IstiaMecatroniqueClub/US_Board/documentation/html/class_hcsr04__coll__graph.png

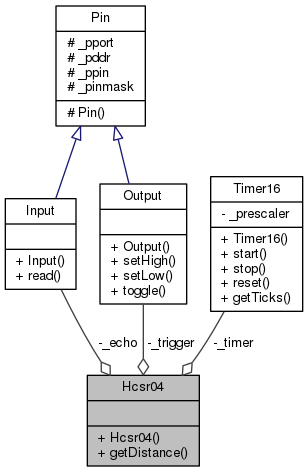
documentation/html/class_hcsr04__coll__graph.png
