IstiaMecatroniqueClub/US_Board/documentation/html/class_pin__inherit__graph.png

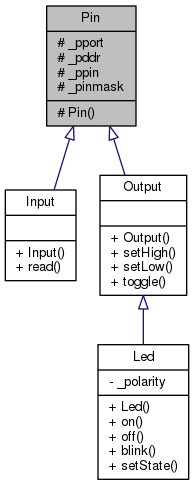
documentation/html/class_pin__inherit__graph.png
