IstiaMecatroniqueClub/US_Board/documentation/html/hcsr04_8cpp__incl.png

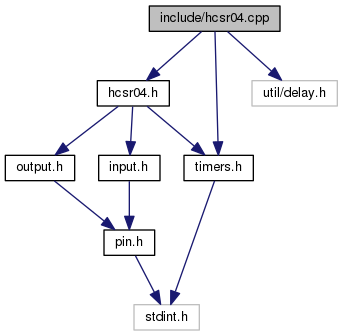
documentation/html/hcsr04_8cpp__incl.png
