IstiaMecatroniqueClub/US_Board/documentation/html/hcsr04_8h__incl.png

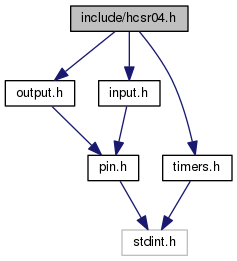
documentation/html/hcsr04_8h__incl.png
