IstiaMecatroniqueClub/US_Board/documentation/html/input_8cpp__incl.png

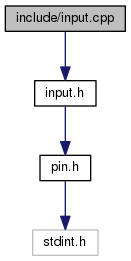
documentation/html/input_8cpp__incl.png
