IstiaMecatroniqueClub/US_Board/documentation/html/input_8h__dep__incl.png

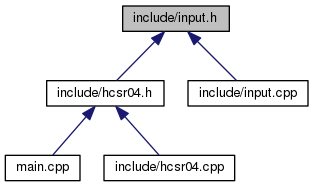
documentation/html/input_8h__dep__incl.png
