IstiaMecatroniqueClub/US_Board/documentation/html/main_8cpp__incl.png

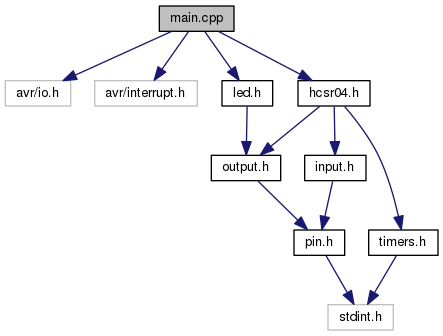
documentation/html/main_8cpp__incl.png
