IstiaMecatroniqueClub/US_Board/documentation/html/output_8h__incl.png

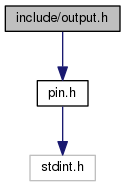
documentation/html/output_8h__incl.png
