IstiaMecatroniqueClub/US_Board/documentation/html/timers_8cpp__incl.png

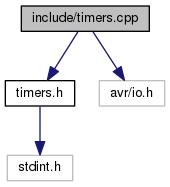
documentation/html/timers_8cpp__incl.png
